Velko/8-bit-CPU/hardware/pcb/register/register.kicad_pcb

## KiCad design hardware/pcb/register/register.kicad_pcb (2020-12-29)

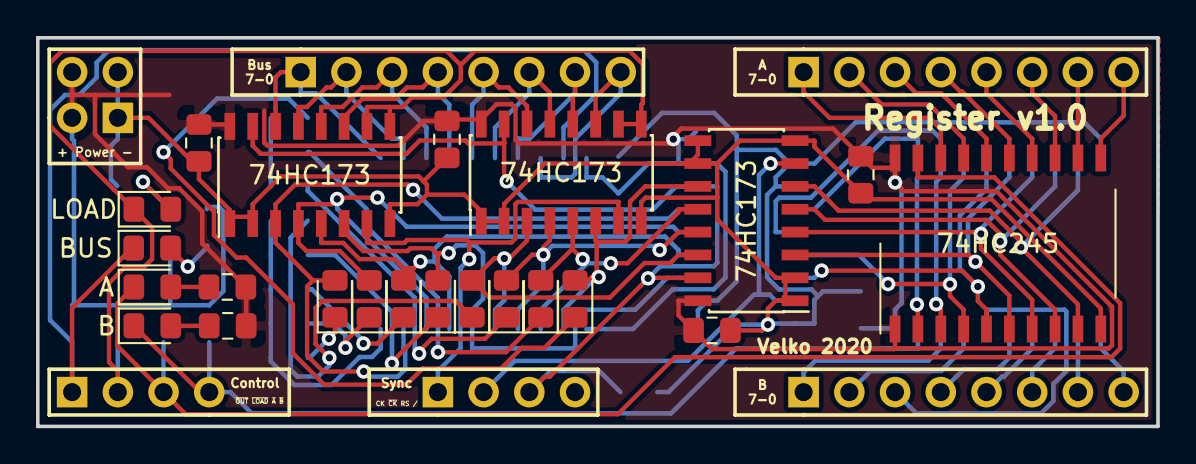
[picture p21: board register.kicad_pcb from above]

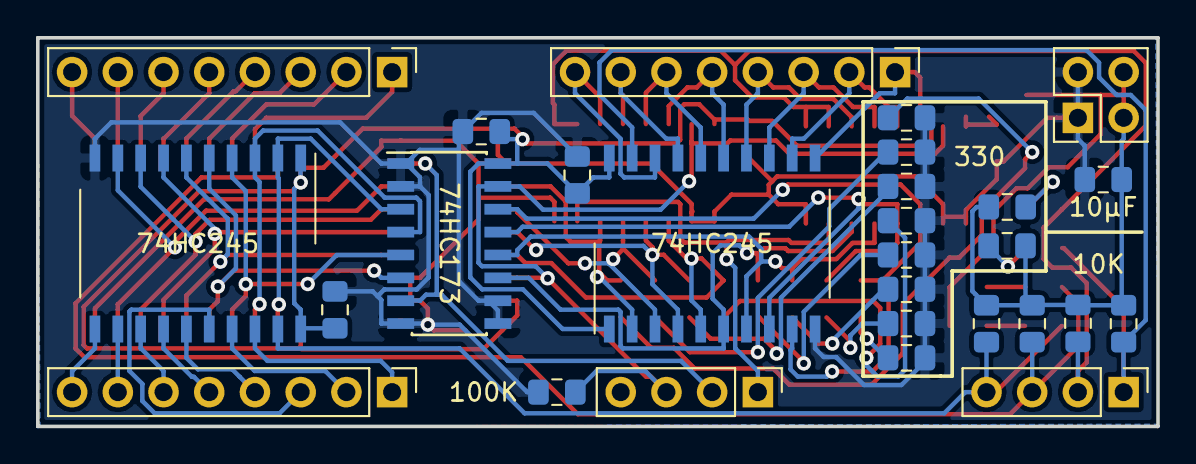
[picture p22: board register.kicad_pcb from below]

Board: 2 copper layers, 62.2 x 21.6 mm, 50 parts (28 on the bottom side), 61 nets.

Parts:
C1, C3, C4, C5, C6, C7, C8: 100nF; C_0805_2012Metric_Pad1.15x1.40mm_HandSolder
C2: 10µF; C_0805_2012Metric_Pad1.15x1.40mm_HandSolder
D1, D2, D3, D4, D5, D6, D7, D8: LED; LED_0805_2012Metric_Pad1.15x1.40mm_HandSolder
D9: LOAD; LED_0805_2012Metric_Pad1.15x1.40mm_HandSolder
D10: BUS; LED_0805_2012Metric_Pad1.15x1.40mm_HandSolder
D11: A; LED_0805_2012Metric_Pad1.15x1.40mm_HandSolder
D12: B; LED_0805_2012Metric_Pad1.15x1.40mm_HandSolder
J1, J5, J6: Conn_01x08_Male; PinHeader_1x08_P2.54mm_Vertical
J2, J3: Conn_01x04_Male; PinHeader_1x04_P2.54mm_Vertical
J4: Conn_01x04_Male; PinHeader_2x02_P2.54mm_Vertical
R1, R2, R3, R4: 10K; R_0805_2012Metric_Pad1.15x1.40mm_HandSolder
R5, R6, R7, R8, R9, R10, R11, R12, R14, R15, R16, R17: 330; R_0805_2012Metric_Pad1.15x1.40mm_HandSolder
R13: 100K; R_0805_2012Metric_Pad1.15x1.40mm_HandSolder
U1, U6, U7: 74HC245; SO-20_12.8x7.5mm_P1.27mm
U2, U3, U4, U5: 74HC173; SOIC-16_3.9x9.9mm_P1.27mm

Connections:
A0: J5.8, U6.11
A1: J5.7, U6.12
A2: J5.6, U6.13
A3: J5.5, U6.14
A4: J5.4, U6.15
A5: J5.3, U6.16
A6: J5.2, U6.17
A7: J5.1, U6.18
B0: J6.8, U7.11
B1: J6.7, U7.12
B2: J6.6, U7.13
B3: J6.5, U7.14
B4: J6.4, U7.15
B5: J6.3, U7.16
B6: J6.2, U7.17
B7: J6.1, U7.18
BUS0: J1.8, U1.18, U2.11
BUS1: J1.7, U1.17, U2.12
BUS2: J1.6, U1.16, U2.13
BUS3: J1.5, U1.15, U2.14
BUS4: J1.4, U1.14, U4.11
BUS5: J1.3, U1.13, U4.12
BUS6: J1.2, U1.12, U4.13
BUS7: J1.1, U1.11, U4.14
CLK: J3.1, U2.7, U4.7
GND: C1.2, C2.2, C3.2, C4.2, C5.2, C6.2, C7.2, C8.2, J4.1, J4.2, R5.1, R6.1, R7.1, R8.1, R9.1, R10.1, R11.1, R12.1, R13.1, U1.10, U2.1, U2.2, U2.8, U3.1, U3.2, U3.8, U3.9, U3.10, U4.1, U4.2, U4.8, U5.1, U5.2, U5.8, U5.9, U5.10, U6.10, U7.10
M0: D1.2, U1.2, U2.6, U3.11
M1: D2.2, U1.3, U2.5, U3.12
M2: D3.2, U1.4, U2.4, U3.13
M3: D4.2, U1.5, U2.3, U3.14
M4: D5.2, U1.6, U4.6, U5.11
M5: D6.2, U1.7, U4.5, U5.12
M6: D7.2, U1.8, U4.4, U5.13
M7: D8.2, U1.9, U4.3, U5.14
unnamed: D1.1, R5.2
unnamed: D2.1, R6.2
unnamed: D3.1, R7.2
unnamed: D4.1, R8.2
unnamed: D5.1, R9.2
unnamed: D6.1, R10.2
unnamed: D7.1, R11.2
unnamed: D8.1, R12.2
unnamed: D9.2, R17.2
unnamed: D10.2, R14.2
unnamed: D11.2, R15.2
unnamed: D12.2, R16.2
RESET: J3.3, R13.2, U2.15, U3.15, U4.15, U5.15
TAP0: U3.6, U6.9, U7.9
TAP1: U3.5, U6.8, U7.8
TAP2: U3.4, U6.7, U7.7
TAP3: U3.3, U6.6, U7.6
TAP4: U5.6, U6.5, U7.5
TAP5: U5.5, U6.4, U7.4
TAP6: U5.4, U6.3, U7.3
TAP7: U5.3, U6.2, U7.2
VCC: C1.1, C2.1, C3.1, C4.1, C5.1, C6.1, C7.1, C8.1, J4.3, J4.4, R1.1, R2.1, R3.2, R4.1, R14.1, R15.1, R16.1, R17.1, U1.1, U1.20, U2.16, U3.16, U4.16, U5.16, U6.1, U6.20, U7.1, U7.20
~A_OUT~: D11.1, J2.3, R2.2, U6.19
~BUS_OUT~: D10.1, J2.1, R1.2, U1.19
~B_OUT~: D12.1, J2.4, R4.2, U7.19
~CLK~: J3.2, U3.7, U5.7
~LOAD~: D9.1, J2.2, R3.1, U2.9, U2.10, U4.9, U4.10
