Velko/8-bit-CPU/hardware/pcb/eeprom_burner/eeprom_burner.kicad_pcb

## KiCad design hardware/pcb/eeprom_burner/eeprom_burner.kicad_pcb (2020-12-29)

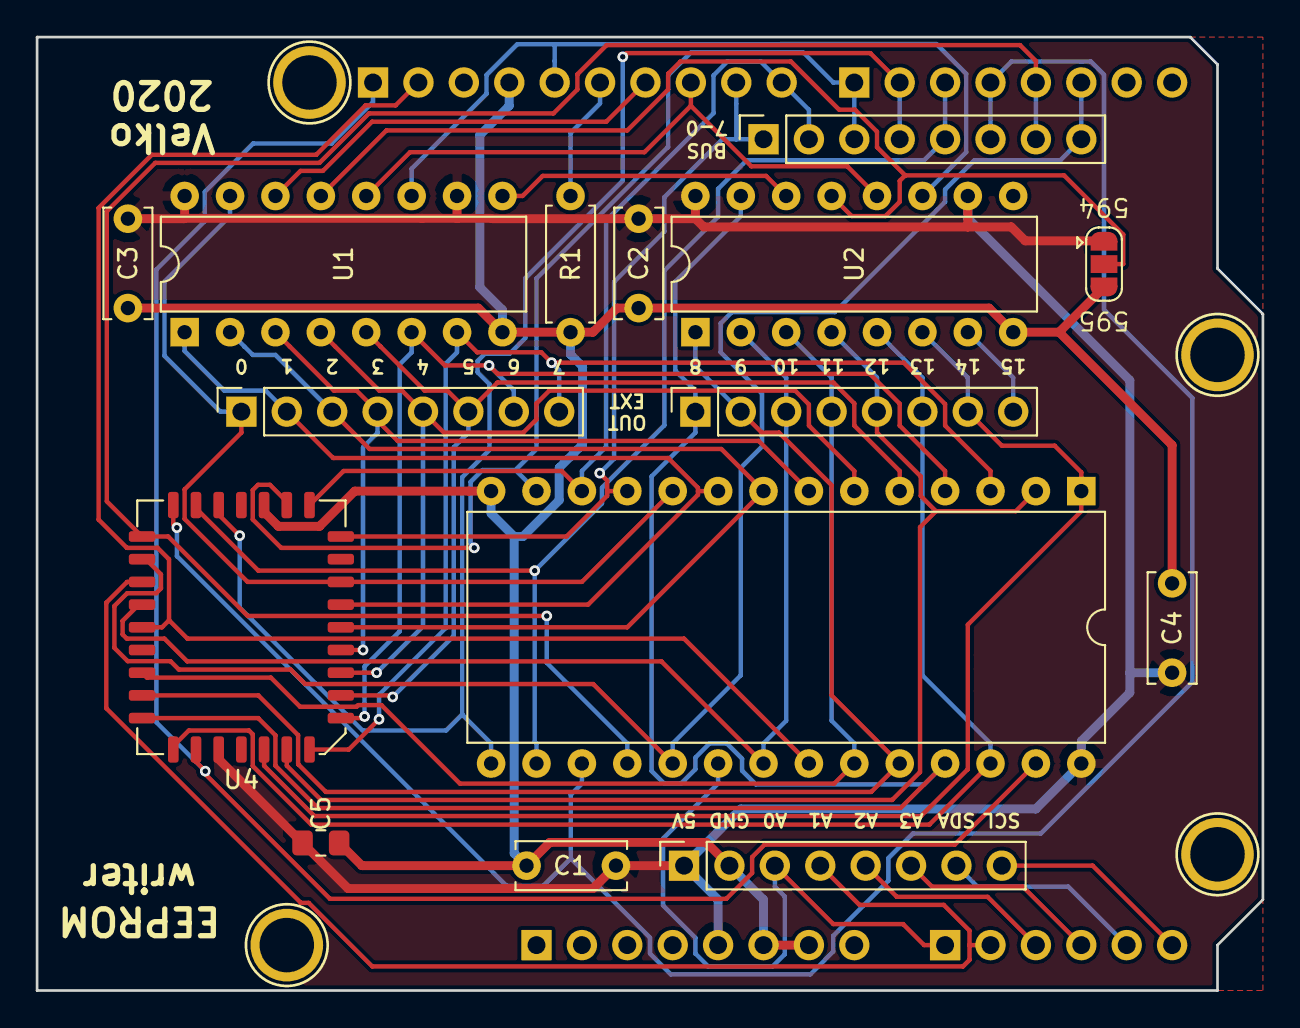
[picture p23: board eeprom_burner.kicad_pcb from above]

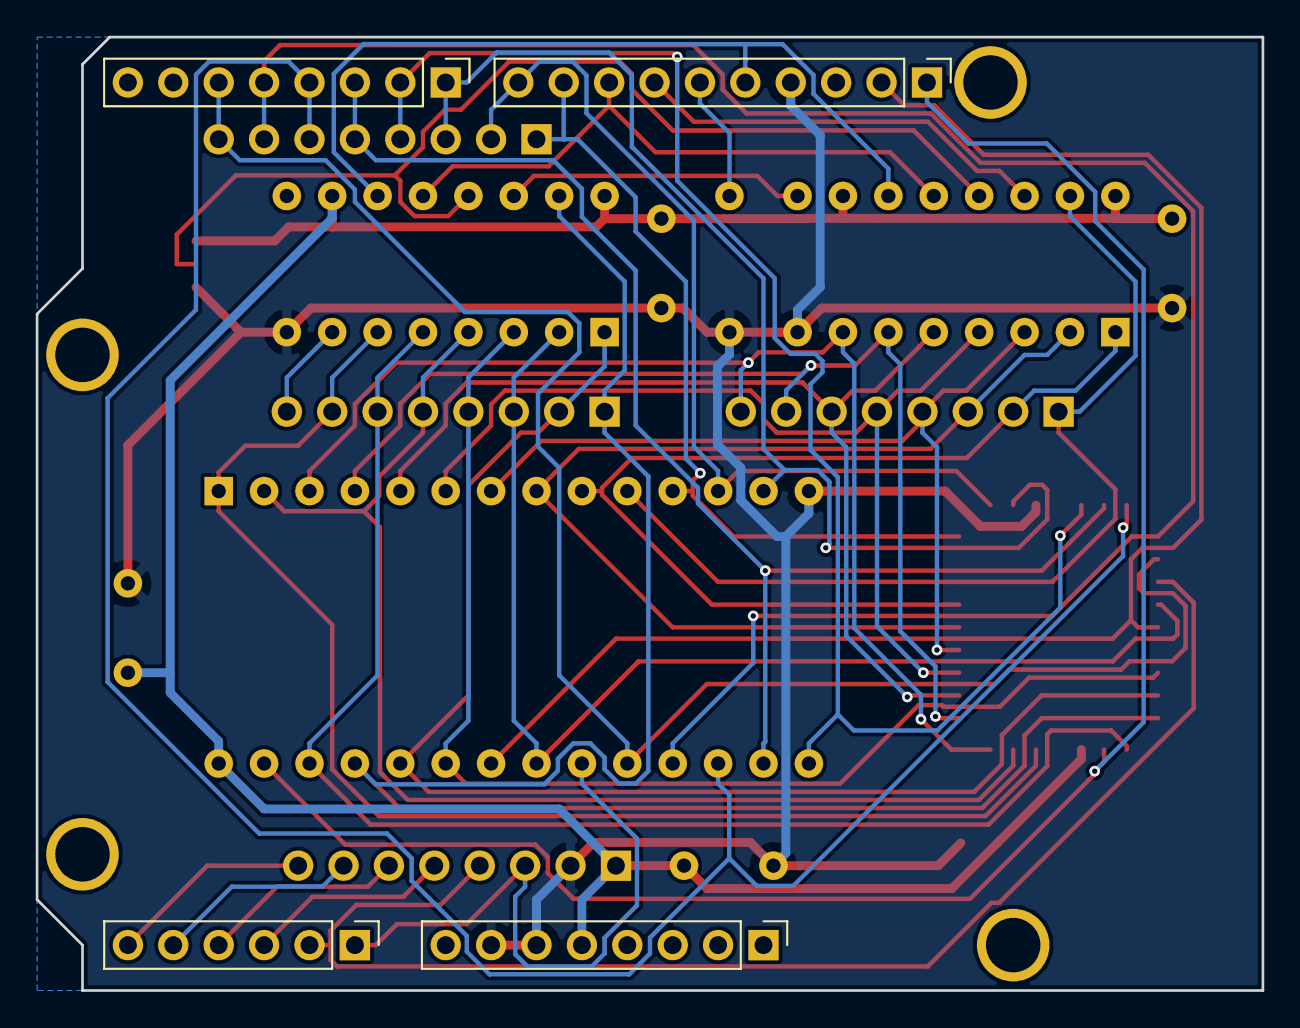
[picture p24: board eeprom_burner.kicad_pcb from below]

Board: 2 copper layers, 68.6 x 53.3 mm, 23 parts (4 on the bottom side), 40 nets.

Parts:
C1, C2, C3, C4: 100nF; C_Disc_D6.0mm_W2.5mm_P5.00mm
C5: 100nF; C_0805_2012Metric_Pad1.15x1.40mm_HandSolder
J1, J2, J3: Conn_01x08; PinSocket_1x08_P2.54mm_Vertical
J4: Conn_01x06; PinSocket_1x08_P2.54mm_Vertical
JP1: SolderJumper_3_Open; SolderJumper-3_P1.3mm_Open_RoundedPad1.0x1.5mm
P1: Power; PinHeader_1x08_P2.54mm_Vertical
P2: Analog; PinHeader_1x06_P2.54mm_Vertical
P3: Digital; PinHeader_1x10_P2.54mm_Vertical
P4: Digital; PinHeader_1x08_P2.54mm_Vertical
P5, P6, P7, P8: CONN_01X01; Arduino_1pin
R1: 10K; R_Axial_DIN0207_L6.3mm_D2.5mm_P7.62mm_Horizontal
U1, U2: 74HC595; DIP-16_W7.62mm
U3: 28C256; DIP-28_W15.24mm
U4: 28C256J; PLCC-32_11.4x14.0mm_P1.27mm

Connections:
+5V: C1.1, C2.1, C3.1, C4.1, C5.1, J4.1, JP1.1, P1.5, U1.10, U1.16, U2.10, U2.16, U3.28, U4.32
A0: J1.1, U1.15, U3.10, U4.11
A1: J1.2, U1.1, U3.9, U4.10
A2: J1.3, U1.2, U3.8, U4.9
A3: J1.4, U1.3, U3.7, U4.8
A4: J1.5, U1.4, U3.6, U4.7
A5: J1.6, U1.5, U3.5, U4.6
A6: J1.7, U1.6, U3.4, U4.5
A7: J1.8, U1.7, U3.3, U4.4
A8: J2.1, U2.15, U3.25, U4.29
A9: J2.2, U2.1, U3.24, U4.28
A10: J2.3, U2.2, U3.21, U4.24
A11: J2.4, U2.3, U3.23, U4.27
A12: J2.5, U2.4, U3.2, U4.3
A13: J2.6, U2.5, U3.26, U4.30
A14: J2.7, U2.6, U3.1, U4.2
A15: J2.8, U2.7
D0: J3.1, P3.9, U3.11, U4.13
D1: J3.2, P3.10, U3.12, U4.14
D2: J3.3, P4.1, U3.13, U4.15
D3: J3.4, P4.2, U3.15, U4.18
D4: J3.5, P4.3, U3.16, U4.19
D5: J3.6, P4.4, U3.17, U4.20
D6: J3.7, P4.5, U3.18, U4.21
D7: J3.8, P4.6, U3.19, U4.22
E0: J4.3, P2.1, U3.20
E1: J4.4, P2.2, U4.23
E2: J4.5, P2.3
E3: J4.6, P2.4
E4: J4.7, P2.5
E5: J4.8, P2.6
GND: C1.2, C2.2, C3.2, C4.2, C5.2, J4.2, JP1.3, P1.6, P1.7, P3.4, R1.2, U1.8, U2.8, U3.14, U4.16
LATCH: P3.8, U1.12, U2.12
MISO: P3.6, R1.1
MOSI: P3.7, U1.14
unnamed: JP1.2, U1.13, U2.13
unnamed: U1.9, U2.14
SCK: P3.5, U1.11, U2.11
~OE~: P3.2, U3.22, U4.25
~WE~: P3.1, U3.27, U4.31
