Velko/8-bit-CPU/hardware/pcb/clock/clock.kicad_pcb

## KiCad design hardware/pcb/clock/clock.kicad_pcb (2020-06-21)

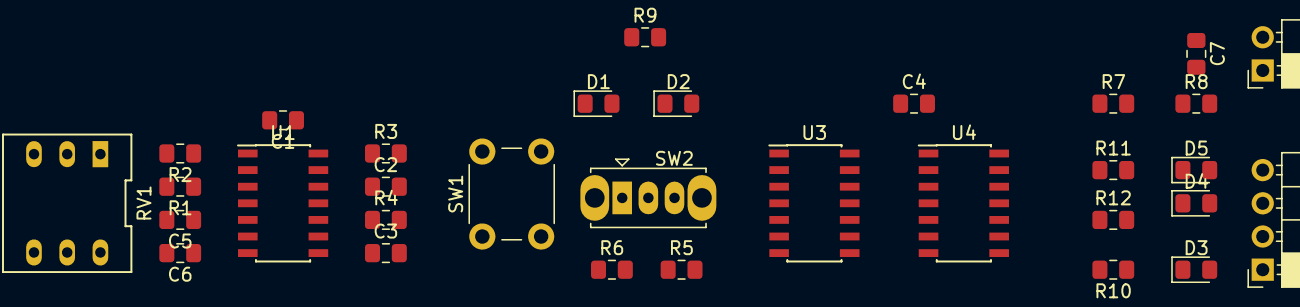
[picture p25: board clock.kicad_pcb from above]

Board: 2 copper layers, 32 parts (0 on the bottom side), 26 nets, no tracks yet.

Parts:
C1, C3, C4, C7: 100nF; C_0805_2012Metric_Pad1.15x1.40mm_HandSolder
C2, C5: 10nF; C_0805_2012Metric_Pad1.15x1.40mm_HandSolder
C6: 1μF; C_0805_2012Metric_Pad1.15x1.40mm_HandSolder
D1, D2, D3, D4, D5: LED; LED_0805_2012Metric_Pad1.15x1.40mm_HandSolder
J1: 01x02_F; PinSocket_1x02_P2.54mm_Horizontal
J2: 01x04_F; PinSocket_1x04_P2.54mm_Horizontal
R1, R2, R3: 1K; R_0805_2012Metric_Pad1.15x1.40mm_HandSolder
R4: 1M; R_0805_2012Metric_Pad1.15x1.40mm_HandSolder
R5, R6, R7, R8: 10K; R_0805_2012Metric_Pad1.15x1.40mm_HandSolder
R9, R10, R11, R12: 330; R_0805_2012Metric_Pad1.15x1.40mm_HandSolder
RV1: 1M; POT_DIP_Dual_Vert
SW1: SW_Push; SW_PUSH_6mm
SW2: SW_SPDT; SW_Slide_1P2T_CK_OS102011MS2Q
U1: TLC556; SOIC-14_3.9x8.7mm_P1.27mm
U3: 74HC02; SOIC-14_3.9x8.7mm_P1.27mm
U4: 74HC00; SOIC-14_3.9x8.7mm_P1.27mm

Connections:
CLK: D3.1, J2.1, U3.5, U3.6, U4.8
GND: C1.2, C2.2, C3.2, C4.2, C5.2, C6.2, C7.2, J1.1, R5.2, R6.2, R8.2, R9.2, R10.2, R11.2, SW1.1, U1.7, U3.2, U3.3, U3.7, U4.7
HLT: D4.1, J2.3, R8.1, U4.13
unnamed: C2.1, U1.11
unnamed: C3.1, R4.2, U1.12, U1.13
unnamed: C5.1, U1.3
unnamed: C6.1, RV1.1, U1.2, U1.6
unnamed: D1.1, U3.9, U3.13, U4.2
unnamed: D1.2, D2.2, R9.1
unnamed: D2.1, U3.10, U3.11, U4.5
unnamed: D3.2, R10.1
unnamed: D4.2, R11.1
unnamed: D5.1, R12.2
unnamed: R1.2, R2.2, U1.1
unnamed: R2.1, RV1.2
unnamed: R3.2, SW1.2, U1.8
unnamed: R5.1, SW2.3, U3.12
unnamed: R6.1, SW2.1, U3.8
unnamed: U1.5, U4.1
unnamed: U1.9, U4.4
unnamed: U1.4, U1.10, U4.11
unnamed: U4.3, U4.9
unnamed: U4.6, U4.10
VCC: C1.1, C4.1, C7.1, J1.2, R1.1, R3.1, R4.1, R7.1, R12.1, SW2.2, U1.14, U3.14, U4.14
~CLK~: J2.2, U3.4
~WAKE~: D5.2, J2.4, R7.2, U4.12
