Velko/8-bit-CPU/turbo/core/src/runtime_state.rs

use crate::{TrapReason, IOPorts};
use crate::flags::Flags;
use crate::router::{MainBusSource, ALULSource, ALURSource, AddressBusSource, FlagsSource};
use crate::router::DeviceMap;

pub struct BusValue<TSource, TValue> {
    pub source: Option<TSource>,
    pub value: TValue,
}

pub struct BusValues {
    pub main_bus: BusValue<MainBusSource, Option<u8>>,
    pub alu_l: BusValue<ALULSource, Option<u8>>,
    pub alu_r: BusValue<ALURSource, Option<u8>>,
    pub address_bus: BusValue<AddressBusSource, Option<u16>>,
    pub flags: BusValue<FlagsSource, ALUFlags>,
    pub injected_main_bus_value: Option<u8>,
    pub injected_address_bus_value: Option<u16>,
    pub th_reg_val: u8,
    pub tl_reg_val: u8,
    pub trap_reason: Option<TrapReason>,
}

impl BusValues {
    pub fn new() -> Self {
        Self {
            main_bus: BusValue { source: None, value: None },
            alu_l: BusValue { source: None, value: None },
            alu_r: BusValue { source: None, value: None },
            address_bus: BusValue { source: None, value: None },
            flags: BusValue { source: None, value: ALUFlags { carry: None, overflow: None } },
            injected_main_bus_value: None,
            injected_address_bus_value: None,
            th_reg_val: 0,
            tl_reg_val: 0,
            trap_reason: None,
        }
    }

    pub fn resolve<P: IOPorts>(&mut self, devices: &DeviceMap<P>) {
        self.alu_l.value = self.alu_l.source.map(|source| devices.get_alu_l_value(source, self));
        self.alu_r.value = self.alu_r.source.map(|source| devices.get_alu_r_value(source, self));
        self.address_bus.value = self.injected_address_bus_value.or_else(|| self.address_bus.source.map(|source| devices.get_address_bus_value(source, self)));
        self.main_bus.value = self.injected_main_bus_value.or_else(|| self.main_bus.source.map(|source| devices.get_main_bus_value(source, self)));
        self.flags.value = self.flags.source.map(|source| devices.get_flags_value(source, self)).unwrap_or(ALUFlags { carry: None, overflow: None });
    }
}

pub struct ALUFlags {
    pub carry: Option<Flags>,
    pub overflow: Option<Flags>,
}
