Velko/8-bit-CPU/emulator/cpu-modules/io_control.v

module io_control (
    inout [7:0] main_bus,
    input rst,
    input clk,

    input loadn,
    input from_devn,
    input to_devn,

    output [7:0] sel_x,
    output [7:0] sel_y,
    output [7:0] sel_p,
    inout [7:0] io_bus
);

    wire [7:0] port_addr;

    dff_377 addr_reg (
        .cp(clk),
        .en(loadn),
        .d(main_bus),
        .q(port_addr)
    );

    demux_138 sel_mux_x (
        .a(port_addr[2:0]),
        .e1n(from_devn && to_devn),
        .e2n(1'b0),
        .e3(1'b1),
        .y(sel_x)
    );

    demux_138 sel_mux_y (
        .a(port_addr[6:4]),
        .e1n(from_devn && to_devn),
        .e2n(1'b0),
        .e3(1'b1),
        .y(sel_y)
    );

    buffer_245 io_buffer (
        .a(main_bus),
        .b(io_bus),
        .dir(from_devn),
        .oen(from_devn && to_devn)
    );

    assign sel_p = port_addr;

endmodule
