Velko/8-bit-CPU/include/microcode.c

#include "microcode.h"

const cword_t op_fetch[] = {0x07bd5889};

const struct op_microcode microcode[] PROGMEM = {

    /* 00 nop        */
    { .default_steps = {0x07ff58ff},},

    /* 01 ldi_A_imm  */
    { .default_steps = {0x07bd5809},},

    /* 02 ldi_B_imm  */
    { .default_steps = {0x07bd5819},},

    /* 03 ldi_C_imm  */
    { .default_steps = {0x07bd5829},},

    /* 04 ldi_D_imm  */
    { .default_steps = {0x07bd5839},},

    /* 05 ldi_F_imm  */
    { .default_steps = {0x07bd5879},},

    /* 06 hlt        */
    { .default_steps = {0x03ff58ff},},

    /* 07 add_A_A    */
    { .default_steps = {0x07ff0005},},

    /* 08 add_A_B    */
    { .default_steps = {0x07ff0405},},

    /* 09 add_A_C    */
    { .default_steps = {0x07ff0805},},

    /* 0a add_A_D    */
    { .default_steps = {0x07ff0c05},},

    /* 0b add_B_A    */
    { .default_steps = {0x07ff0115},},

    /* 0c add_B_B    */
    { .default_steps = {0x07ff0515},},

    /* 0d add_B_C    */
    { .default_steps = {0x07ff0915},},

    /* 0e add_B_D    */
    { .default_steps = {0x07ff0d15},},

    /* 0f add_C_A    */
    { .default_steps = {0x07ff0225},},

    /* 10 add_C_B    */
    { .default_steps = {0x07ff0625},},

    /* 11 add_C_C    */
    { .default_steps = {0x07ff0a25},},

    /* 12 add_C_D    */
    { .default_steps = {0x07ff0e25},},

    /* 13 add_D_A    */
    { .default_steps = {0x07ff0335},},

    /* 14 add_D_B    */
    { .default_steps = {0x07ff0735},},

    /* 15 add_D_C    */
    { .default_steps = {0x07ff0b35},},

    /* 16 add_D_D    */
    { .default_steps = {0x07ff0f35},},

    /* 17 adc_A_A    */
    { .default_steps = {0x07ff0005},
      .f_alt = {
          /* mask: -C-- value: -C-- */
          { .mask = 0x04, .value = 0x04,
            .steps = {0x07ff8005},
          },
      },
    },

    /* 18 adc_A_B    */
    { .default_steps = {0x07ff0405},
      .f_alt = {
          /* mask: -C-- value: -C-- */
          { .mask = 0x04, .value = 0x04,
            .steps = {0x07ff8405},
          },
      },
    },

    /* 19 adc_A_C    */
    { .default_steps = {0x07ff0805},
      .f_alt = {
          /* mask: -C-- value: -C-- */
          { .mask = 0x04, .value = 0x04,
            .steps = {0x07ff8805},
          },
      },
    },

    /* 1a adc_A_D    */
    { .default_steps = {0x07ff0c05},
      .f_alt = {
          /* mask: -C-- value: -C-- */
          { .mask = 0x04, .value = 0x04,
            .steps = {0x07ff8c05},
          },
      },
    },

    /* 1b adc_B_A    */
    { .default_steps = {0x07ff0115},
      .f_alt = {
          /* mask: -C-- value: -C-- */
          { .mask = 0x04, .value = 0x04,
            .steps = {0x07ff8115},
          },
      },
    },

    /* 1c adc_B_B    */
    { .default_steps = {0x07ff0515},
      .f_alt = {
          /* mask: -C-- value: -C-- */
          { .mask = 0x04, .value = 0x04,
            .steps = {0x07ff8515},
          },
      },
    },

    /* 1d adc_B_C    */
    { .default_steps = {0x07ff0915},
      .f_alt = {
          /* mask: -C-- value: -C-- */
          { .mask = 0x04, .value = 0x04,
            .steps = {0x07ff8915},
          },
      },
    },

    /* 1e adc_B_D    */
    { .default_steps = {0x07ff0d15},
      .f_alt = {
          /* mask: -C-- value: -C-- */
          { .mask = 0x04, .value = 0x04,
            .steps = {0x07ff8d15},
          },
      },
    },

    /* 1f adc_C_A    */
    { .default_steps = {0x07ff0225},
      .f_alt = {
          /* mask: -C-- value: -C-- */
          { .mask = 0x04, .value = 0x04,
            .steps = {0x07ff8225},
          },
      },
    },

    /* 20 adc_C_B    */
    { .default_steps = {0x07ff0625},
      .f_alt = {
          /* mask: -C-- value: -C-- */
          { .mask = 0x04, .value = 0x04,
            .steps = {0x07ff8625},
          },
      },
    },

    /* 21 adc_C_C    */
    { .default_steps = {0x07ff0a25},
      .f_alt = {
          /* mask: -C-- value: -C-- */
          { .mask = 0x04, .value = 0x04,
            .steps = {0x07ff8a25},
          },
      },
    },

    /* 22 adc_C_D    */
    { .default_steps = {0x07ff0e25},
      .f_alt = {
          /* mask: -C-- value: -C-- */
          { .mask = 0x04, .value = 0x04,
            .steps = {0x07ff8e25},
          },
      },
    },

    /* 23 adc_D_A    */
    { .default_steps = {0x07ff0335},
      .f_alt = {
          /* mask: -C-- value: -C-- */
          { .mask = 0x04, .value = 0x04,
            .steps = {0x07ff8335},
          },
      },
    },

    /* 24 adc_D_B    */
    { .default_steps = {0x07ff0735},
      .f_alt = {
          /* mask: -C-- value: -C-- */
          { .mask = 0x04, .value = 0x04,
            .steps = {0x07ff8735},
          },
      },
    },

    /* 25 adc_D_C    */
    { .default_steps = {0x07ff0b35},
      .f_alt = {
          /* mask: -C-- value: -C-- */
          { .mask = 0x04, .value = 0x04,
            .steps = {0x07ff8b35},
          },
      },
    },

    /* 26 adc_D_D    */
    { .default_steps = {0x07ff0f35},
      .f_alt = {
          /* mask: -C-- value: -C-- */
          { .mask = 0x04, .value = 0x04,
            .steps = {0x07ff8f35},
          },
      },
    },

    /* 27 sub_A_B    */
    { .default_steps = {0x07ff2405},},

    /* 28 sub_A_C    */
    { .default_steps = {0x07ff2805},},

    /* 29 sub_A_D    */
    { .default_steps = {0x07ff2c05},},

    /* 2a sub_B_A    */
    { .default_steps = {0x07ff2115},},

    /* 2b sub_B_C    */
    { .default_steps = {0x07ff2915},},

    /* 2c sub_B_D    */
    { .default_steps = {0x07ff2d15},},

    /* 2d sub_C_A    */
    { .default_steps = {0x07ff2225},},

    /* 2e sub_C_B    */
    { .default_steps = {0x07ff2625},},

    /* 2f sub_C_D    */
    { .default_steps = {0x07ff2e25},},

    /* 30 sub_D_A    */
    { .default_steps = {0x07ff2335},},

    /* 31 sub_D_B    */
    { .default_steps = {0x07ff2735},},

    /* 32 sub_D_C    */
    { .default_steps = {0x07ff2b35},},

    /* 33 sbb_A_B    */
    { .default_steps = {0x07ff2405},
      .f_alt = {
          /* mask: -C-- value: -C-- */
          { .mask = 0x04, .value = 0x04,
            .steps = {0x07ffa405},
          },
      },
    },

    /* 34 sbb_A_C    */
    { .default_steps = {0x07ff2805},
      .f_alt = {
          /* mask: -C-- value: -C-- */
          { .mask = 0x04, .value = 0x04,
            .steps = {0x07ffa805},
          },
      },
    },

    /* 35 sbb_A_D    */
    { .default_steps = {0x07ff2c05},
      .f_alt = {
          /* mask: -C-- value: -C-- */
          { .mask = 0x04, .value = 0x04,
            .steps = {0x07ffac05},
          },
      },
    },

    /* 36 sbb_B_A    */
    { .default_steps = {0x07ff2115},
      .f_alt = {
          /* mask: -C-- value: -C-- */
          { .mask = 0x04, .value = 0x04,
            .steps = {0x07ffa115},
          },
      },
    },

    /* 37 sbb_B_C    */
    { .default_steps = {0x07ff2915},
      .f_alt = {
          /* mask: -C-- value: -C-- */
          { .mask = 0x04, .value = 0x04,
            .steps = {0x07ffa915},
          },
      },
    },

    /* 38 sbb_B_D    */
    { .default_steps = {0x07ff2d15},
      .f_alt = {
          /* mask: -C-- value: -C-- */
          { .mask = 0x04, .value = 0x04,
            .steps = {0x07ffad15},
          },
      },
    },

    /* 39 sbb_C_A    */
    { .default_steps = {0x07ff2225},
      .f_alt = {
          /* mask: -C-- value: -C-- */
          { .mask = 0x04, .value = 0x04,
            .steps = {0x07ffa225},
          },
      },
    },

    /* 3a sbb_C_B    */
    { .default_steps = {0x07ff2625},
      .f_alt = {
          /* mask: -C-- value: -C-- */
          { .mask = 0x04, .value = 0x04,
            .steps = {0x07ffa625},
          },
      },
    },

    /* 3b sbb_C_D    */
    { .default_steps = {0x07ff2e25},
      .f_alt = {
          /* mask: -C-- value: -C-- */
          { .mask = 0x04, .value = 0x04,
            .steps = {0x07ffae25},
          },
      },
    },

    /* 3c sbb_D_A    */
    { .default_steps = {0x07ff2335},
      .f_alt = {
          /* mask: -C-- value: -C-- */
          { .mask = 0x04, .value = 0x04,
            .steps = {0x07ffa335},
          },
      },
    },

    /* 3d sbb_D_B    */
    { .default_steps = {0x07ff2735},
      .f_alt = {
          /* mask: -C-- value: -C-- */
          { .mask = 0x04, .value = 0x04,
            .steps = {0x07ffa735},
          },
      },
    },

    /* 3e sbb_D_C    */
    { .default_steps = {0x07ff2b35},
      .f_alt = {
          /* mask: -C-- value: -C-- */
          { .mask = 0x04, .value = 0x04,
            .steps = {0x07ffab35},
          },
      },
    },

    /* 3f and_A_B    */
    { .default_steps = {0x07ff0406},},

    /* 40 and_A_C    */
    { .default_steps = {0x07ff0806},},

    /* 41 and_A_D    */
    { .default_steps = {0x07ff0c06},},

    /* 42 and_B_A    */
    { .default_steps = {0x07ff0116},},

    /* 43 and_B_C    */
    { .default_steps = {0x07ff0916},},

    /* 44 and_B_D    */
    { .default_steps = {0x07ff0d16},},

    /* 45 and_C_A    */
    { .default_steps = {0x07ff0226},},

    /* 46 and_C_B    */
    { .default_steps = {0x07ff0626},},

    /* 47 and_C_D    */
    { .default_steps = {0x07ff0e26},},

    /* 48 and_D_A    */
    { .default_steps = {0x07ff0336},},

    /* 49 and_D_B    */
    { .default_steps = {0x07ff0736},},

    /* 4a and_D_C    */
    { .default_steps = {0x07ff0b36},},

    /* 4b or_A_B     */
    { .default_steps = {0x07ff040d},},

    /* 4c or_A_C     */
    { .default_steps = {0x07ff080d},},

    /* 4d or_A_D     */
    { .default_steps = {0x07ff0c0d},},

    /* 4e or_B_A     */
    { .default_steps = {0x07ff011d},},

    /* 4f or_B_C     */
    { .default_steps = {0x07ff091d},},

    /* 50 or_B_D     */
    { .default_steps = {0x07ff0d1d},},

    /* 51 or_C_A     */
    { .default_steps = {0x07ff022d},},

    /* 52 or_C_B     */
    { .default_steps = {0x07ff062d},},

    /* 53 or_C_D     */
    { .default_steps = {0x07ff0e2d},},

    /* 54 or_D_A     */
    { .default_steps = {0x07ff033d},},

    /* 55 or_D_B     */
    { .default_steps = {0x07ff073d},},

    /* 56 or_D_C     */
    { .default_steps = {0x07ff0b3d},},

    /* 57 xor_A_B    */
    { .default_steps = {0x07ff040a},},

    /* 58 xor_A_C    */
    { .default_steps = {0x07ff080a},},

    /* 59 xor_A_D    */
    { .default_steps = {0x07ff0c0a},},

    /* 5a xor_B_A    */
    { .default_steps = {0x07ff011a},},

    /* 5b xor_B_C    */
    { .default_steps = {0x07ff091a},},

    /* 5c xor_B_D    */
    { .default_steps = {0x07ff0d1a},},

    /* 5d xor_C_A    */
    { .default_steps = {0x07ff022a},},

    /* 5e xor_C_B    */
    { .default_steps = {0x07ff062a},},

    /* 5f xor_C_D    */
    { .default_steps = {0x07ff0e2a},},

    /* 60 xor_D_A    */
    { .default_steps = {0x07ff033a},},

    /* 61 xor_D_B    */
    { .default_steps = {0x07ff073a},},

    /* 62 xor_D_C    */
    { .default_steps = {0x07ff0b3a},},

    /* 63 not_A      */
    { .default_steps = {0x07ff140a},},

    /* 64 not_B      */
    { .default_steps = {0x07ff151a},},

    /* 65 not_C      */
    { .default_steps = {0x07ff162a},},

    /* 66 not_D      */
    { .default_steps = {0x07ff173a},},

    /* 67 clr_A      */
    { .default_steps = {0x07ff000a},},

    /* 68 clr_B      */
    { .default_steps = {0x07ff051a},},

    /* 69 clr_C      */
    { .default_steps = {0x07ff0a2a},},

    /* 6a clr_D      */
    { .default_steps = {0x07ff0f3a},},

    /* 6b inc_A      */
    { .default_steps = {0x07ff9805},},

    /* 6c inc_B      */
    { .default_steps = {0x07ff9915},},

    /* 6d inc_C      */
    { .default_steps = {0x07ff9a25},},

    /* 6e inc_D      */
    { .default_steps = {0x07ff9b35},},

    /* 6f dec_A      */
    { .default_steps = {0x07ffb805},},

    /* 70 dec_B      */
    { .default_steps = {0x07ffb915},},

    /* 71 dec_C      */
    { .default_steps = {0x07ffba25},},

    /* 72 dec_D      */
    { .default_steps = {0x07ffbb35},},

    /* 73 shr_A      */
    { .default_steps = {0x07ff1807},},

    /* 74 shr_B      */
    { .default_steps = {0x07ff1917},},

    /* 75 shr_C      */
    { .default_steps = {0x07ff1a27},},

    /* 76 shr_D      */
    { .default_steps = {0x07ff1b37},},

    /* 77 ror_A      */
    { .default_steps = {0x07ff1807},
      .f_alt = {
          /* mask: -C-- value: -C-- */
          { .mask = 0x04, .value = 0x04,
            .steps = {0x07ff9807},
          },
      },
    },

    /* 78 ror_B      */
    { .default_steps = {0x07ff1917},
      .f_alt = {
          /* mask: -C-- value: -C-- */
          { .mask = 0x04, .value = 0x04,
            .steps = {0x07ff9917},
          },
      },
    },

    /* 79 ror_C      */
    { .default_steps = {0x07ff1a27},
      .f_alt = {
          /* mask: -C-- value: -C-- */
          { .mask = 0x04, .value = 0x04,
            .steps = {0x07ff9a27},
          },
      },
    },

    /* 7a ror_D      */
    { .default_steps = {0x07ff1b37},
      .f_alt = {
          /* mask: -C-- value: -C-- */
          { .mask = 0x04, .value = 0x04,
            .steps = {0x07ff9b37},
          },
      },
    },

    /* 7b asr_A      */
    { .default_steps = {0x07ff18f0, 0x07ff1807},
      .f_alt = {
          /* mask: ---N value: ---N */
          { .mask = 0x01, .value = 0x01,
            .steps = {0x07ff18f0, 0x07ff9807},
          },
      },
    },

    /* 7c asr_B      */
    { .default_steps = {0x07ff18f1, 0x07ff1917},
      .f_alt = {
          /* mask: ---N value: ---N */
          { .mask = 0x01, .value = 0x01,
            .steps = {0x07ff18f1, 0x07ff9917},
          },
      },
    },

    /* 7d asr_C      */
    { .default_steps = {0x07ff18f2, 0x07ff1a27},
      .f_alt = {
          /* mask: ---N value: ---N */
          { .mask = 0x01, .value = 0x01,
            .steps = {0x07ff18f2, 0x07ff9a27},
          },
      },
    },

    /* 7e asr_D      */
    { .default_steps = {0x07ff18f3, 0x07ff1b37},
      .f_alt = {
          /* mask: ---N value: ---N */
          { .mask = 0x01, .value = 0x01,
            .steps = {0x07ff18f3, 0x07ff9b37},
          },
      },
    },

    /* 7f swap_A     */
    { .default_steps = {0x07ff180e},},

    /* 80 swap_B     */
    { .default_steps = {0x07ff191e},},

    /* 81 swap_C     */
    { .default_steps = {0x07ff1a2e},},

    /* 82 swap_D     */
    { .default_steps = {0x07ff1b3e},},

    /* 83 cmp_A_B    */
    { .default_steps = {0x07ff24f5},},

    /* 84 cmp_A_C    */
    { .default_steps = {0x07ff28f5},},

    /* 85 cmp_A_D    */
    { .default_steps = {0x07ff2cf5},},

    /* 86 cmp_B_A    */
    { .default_steps = {0x07ff21f5},},

    /* 87 cmp_B_C    */
    { .default_steps = {0x07ff29f5},},

    /* 88 cmp_B_D    */
    { .default_steps = {0x07ff2df5},},

    /* 89 cmp_C_A    */
    { .default_steps = {0x07ff22f5},},

    /* 8a cmp_C_B    */
    { .default_steps = {0x07ff26f5},},

    /* 8b cmp_C_D    */
    { .default_steps = {0x07ff2ef5},},

    /* 8c cmp_D_A    */
    { .default_steps = {0x07ff23f5},},

    /* 8d cmp_D_B    */
    { .default_steps = {0x07ff27f5},},

    /* 8e cmp_D_C    */
    { .default_steps = {0x07ff2bf5},},

    /* 8f mov_A_B    */
    { .default_steps = {0x07ff5801},},

    /* 90 mov_A_C    */
    { .default_steps = {0x07ff5802},},

    /* 91 mov_A_D    */
    { .default_steps = {0x07ff5803},},

    /* 92 mov_B_A    */
    { .default_steps = {0x07ff5810},},

    /* 93 mov_B_C    */
    { .default_steps = {0x07ff5812},},

    /* 94 mov_B_D    */
    { .default_steps = {0x07ff5813},},

    /* 95 mov_C_A    */
    { .default_steps = {0x07ff5820},},

    /* 96 mov_C_B    */
    { .default_steps = {0x07ff5821},},

    /* 97 mov_C_D    */
    { .default_steps = {0x07ff5823},},

    /* 98 mov_D_A    */
    { .default_steps = {0x07ff5830},},

    /* 99 mov_D_B    */
    { .default_steps = {0x07ff5831},},

    /* 9a mov_D_C    */
    { .default_steps = {0x07ff5832},},

    /* 9b out_imm_A  */
    { .default_steps = {0x07bd5849, 0x07ff5850},},

    /* 9c out_imm_B  */
    { .default_steps = {0x07bd5849, 0x07ff5851},},

    /* 9d out_imm_C  */
    { .default_steps = {0x07bd5849, 0x07ff5852},},

    /* 9e out_imm_D  */
    { .default_steps = {0x07bd5849, 0x07ff5853},},

    /* 9f in_A_imm   */
    { .default_steps = {0x07bd5849, 0x07ff1808},},

    /* a0 in_B_imm   */
    { .default_steps = {0x07bd5849, 0x07ff1818},},

    /* a1 in_C_imm   */
    { .default_steps = {0x07bd5849, 0x07ff1828},},

    /* a2 in_D_imm   */
    { .default_steps = {0x07bd5849, 0x07ff1838},},

    /* a3 st_addr_A  */
    { .default_steps = {0x07bd58b9, 0x07bd58c9, 0x07f85890},},

    /* a4 st_addr_B  */
    { .default_steps = {0x07bd58b9, 0x07bd58c9, 0x07f85891},},

    /* a5 st_addr_C  */
    { .default_steps = {0x07bd58b9, 0x07bd58c9, 0x07f85892},},

    /* a6 st_addr_D  */
    { .default_steps = {0x07bd58b9, 0x07bd58c9, 0x07f85893},},

    /* a7 st_TDP_A_A */
    { .default_steps = {0x07d658f0, 0x07fa5890},},

    /* a8 st_TDP_A_B */
    { .default_steps = {0x07d658f0, 0x07fa5891},},

    /* a9 st_TDP_A_C */
    { .default_steps = {0x07d658f0, 0x07fa5892},},

    /* aa st_TDP_A_D */
    { .default_steps = {0x07d658f0, 0x07fa5893},},

    /* ab st_TDP_B_A */
    { .default_steps = {0x07d658f1, 0x07fa5890},},

    /* ac st_TDP_B_B */
    { .default_steps = {0x07d658f1, 0x07fa5891},},

    /* ad st_TDP_B_C */
    { .default_steps = {0x07d658f1, 0x07fa5892},},

    /* ae st_TDP_B_D */
    { .default_steps = {0x07d658f1, 0x07fa5893},},

    /* af st_TDP_C_A */
    { .default_steps = {0x07d658f2, 0x07fa5890},},

    /* b0 st_TDP_C_B */
    { .default_steps = {0x07d658f2, 0x07fa5891},},

    /* b1 st_TDP_C_C */
    { .default_steps = {0x07d658f2, 0x07fa5892},},

    /* b2 st_TDP_C_D */
    { .default_steps = {0x07d658f2, 0x07fa5893},},

    /* b3 st_TDP_D_A */
    { .default_steps = {0x07d658f3, 0x07fa5890},},

    /* b4 st_TDP_D_B */
    { .default_steps = {0x07d658f3, 0x07fa5891},},

    /* b5 st_TDP_D_C */
    { .default_steps = {0x07d658f3, 0x07fa5892},},

    /* b6 st_TDP_D_D */
    { .default_steps = {0x07d658f3, 0x07fa5893},},

    /* b7 ld_A_addr  */
    { .default_steps = {0x07bd58b9, 0x07bd58c9, 0x07f81809},},

    /* b8 ld_B_addr  */
    { .default_steps = {0x07bd58b9, 0x07bd58c9, 0x07f81819},},

    /* b9 ld_C_addr  */
    { .default_steps = {0x07bd58b9, 0x07bd58c9, 0x07f81829},},

    /* ba ld_D_addr  */
    { .default_steps = {0x07bd58b9, 0x07bd58c9, 0x07f81839},},

    /* bb ld_A_SDP_A */
    { .default_steps = {0x07d158f0, 0x07fa1809},},

    /* bc ld_A_SDP_B */
    { .default_steps = {0x07d158f1, 0x07fa1809},},

    /* bd ld_A_SDP_C */
    { .default_steps = {0x07d158f2, 0x07fa1809},},

    /* be ld_A_SDP_D */
    { .default_steps = {0x07d158f3, 0x07fa1809},},

    /* bf ld_B_SDP_A */
    { .default_steps = {0x07d158f0, 0x07fa1819},},

    /* c0 ld_B_SDP_B */
    { .default_steps = {0x07d158f1, 0x07fa1819},},

    /* c1 ld_B_SDP_C */
    { .default_steps = {0x07d158f2, 0x07fa1819},},

    /* c2 ld_B_SDP_D */
    { .default_steps = {0x07d158f3, 0x07fa1819},},

    /* c3 ld_C_SDP_A */
    { .default_steps = {0x07d158f0, 0x07fa1829},},

    /* c4 ld_C_SDP_B */
    { .default_steps = {0x07d158f1, 0x07fa1829},},

    /* c5 ld_C_SDP_C */
    { .default_steps = {0x07d158f2, 0x07fa1829},},

    /* c6 ld_C_SDP_D */
    { .default_steps = {0x07d158f3, 0x07fa1829},},

    /* c7 ld_D_SDP_A */
    { .default_steps = {0x07d158f0, 0x07fa1839},},

    /* c8 ld_D_SDP_B */
    { .default_steps = {0x07d158f1, 0x07fa1839},},

    /* c9 ld_D_SDP_C */
    { .default_steps = {0x07d158f2, 0x07fa1839},},

    /* ca ld_D_SDP_D */
    { .default_steps = {0x07d158f3, 0x07fa1839},},

    /* cb st_TDP_A   */
    { .default_steps = {0x07be5890},},

    /* cc st_TDP_B   */
    { .default_steps = {0x07be5891},},

    /* cd st_TDP_C   */
    { .default_steps = {0x07be5892},},

    /* ce st_TDP_D   */
    { .default_steps = {0x07be5893},},

    /* cf jmp_addr   */
    { .default_steps = {0x07bd58b9, 0x07bd58c9, 0x07e858ff},},

    /* d0 beq_addr   */
    { .default_steps = {0x07bd58ff, 0x07bd58ff},
      .f_alt = {
          /* mask: --Z- value: --Z- */
          { .mask = 0x02, .value = 0x02,
            .steps = {0x07bd58b9, 0x07bd58c9, 0x07e858ff},
          },
      },
    },

    /* d1 bne_addr   */
    { .default_steps = {0x07bd58ff, 0x07bd58ff},
      .f_alt = {
          /* mask: --Z- value: ---- */
          { .mask = 0x02, .value = 0x00,
            .steps = {0x07bd58b9, 0x07bd58c9, 0x07e858ff},
          },
      },
    },

    /* d2 bcs_addr   */
    { .default_steps = {0x07bd58ff, 0x07bd58ff},
      .f_alt = {
          /* mask: -C-- value: -C-- */
          { .mask = 0x04, .value = 0x04,
            .steps = {0x07bd58b9, 0x07bd58c9, 0x07e858ff},
          },
      },
    },

    /* d3 bcc_addr   */
    { .default_steps = {0x07bd58ff, 0x07bd58ff},
      .f_alt = {
          /* mask: -C-- value: ---- */
          { .mask = 0x04, .value = 0x00,
            .steps = {0x07bd58b9, 0x07bd58c9, 0x07e858ff},
          },
      },
    },

    /* d4 bmi_addr   */
    { .default_steps = {0x07bd58ff, 0x07bd58ff},
      .f_alt = {
          /* mask: ---N value: ---N */
          { .mask = 0x01, .value = 0x01,
            .steps = {0x07bd58b9, 0x07bd58c9, 0x07e858ff},
          },
      },
    },

    /* d5 bpl_addr   */
    { .default_steps = {0x07bd58ff, 0x07bd58ff},
      .f_alt = {
          /* mask: ---N value: ---- */
          { .mask = 0x01, .value = 0x00,
            .steps = {0x07bd58b9, 0x07bd58c9, 0x07e858ff},
          },
      },
    },

    /* d6 push_A     */
    { .default_steps = {0x077b58ff, 0x07fb5890},},

    /* d7 push_B     */
    { .default_steps = {0x077b58ff, 0x07fb5891},},

    /* d8 push_C     */
    { .default_steps = {0x077b58ff, 0x07fb5892},},

    /* d9 push_D     */
    { .default_steps = {0x077b58ff, 0x07fb5893},},

    /* da push_F     */
    { .default_steps = {0x077b58ff, 0x07fb5894},},

    /* db push_LR    */
    { .default_steps = {0x07c458ff, 0x077b58ff, 0x077b589c, 0x07fb589b},},

    /* dc pop_A      */
    { .default_steps = {0x07bb5809},},

    /* dd pop_B      */
    { .default_steps = {0x07bb5819},},

    /* de pop_C      */
    { .default_steps = {0x07bb5829},},

    /* df pop_D      */
    { .default_steps = {0x07bb5839},},

    /* e0 pop_F      */
    { .default_steps = {0x07bb5879},},

    /* e1 pop_LR     */
    { .default_steps = {0x07bb58b9, 0x07bb58c9, 0x07e058ff},},

    /* e2 call_addr  */
    { .default_steps = {0x07bd58b9, 0x07bd58c9, 0x07e558ff, 0x07e858ff},},

    /* e3 ret        */
    { .default_steps = {0x07ec58ff},},

    /* e4 brk        */
    { .default_steps = {0x0fff58ff},},

    /* e5 lea_SP_addr */
    { .default_steps = {0x07bd58b9, 0x07bd58c9, 0x07d858ff},},

    /* e6 ld_A_SP_imm */
    { .default_steps = {0x07bd58b9, 0x17d358fb, 0x07fa1809},},

    /* e7 ld_B_SP_imm */
    { .default_steps = {0x07bd58b9, 0x17d358fb, 0x07fa1819},},

    /* e8 ld_C_SP_imm */
    { .default_steps = {0x07bd58b9, 0x17d358fb, 0x07fa1829},},

    /* e9 ld_D_SP_imm */
    { .default_steps = {0x07bd58b9, 0x17d358fb, 0x07fa1839},},

    /* ea st_SP_imm_A */
    { .default_steps = {0x07bd58b9, 0x17d358fb, 0x07fa5890},},

    /* eb st_SP_imm_B */
    { .default_steps = {0x07bd58b9, 0x17d358fb, 0x07fa5891},},

    /* ec st_SP_imm_C */
    { .default_steps = {0x07bd58b9, 0x17d358fb, 0x07fa5892},},

    /* ed st_SP_imm_D */
    { .default_steps = {0x07bd58b9, 0x17d358fb, 0x07fa5893},},

    /* ee xprefix    */
    { .default_steps = {0x05bd5889, 0x07ff58ff},},

    /* ef jmp_pcrel  */
    { .default_steps = {0x179558f9, 0x07ea58ff},},

    /* f0 beq_pcrel  */
    { .default_steps = {0x07bd58ff},
      .f_alt = {
          /* mask: --Z- value: --Z- */
          { .mask = 0x02, .value = 0x02,
            .steps = {0x179558f9, 0x07ea58ff},
          },
      },
    },

    /* f1 bne_pcrel  */
    { .default_steps = {0x07bd58ff},
      .f_alt = {
          /* mask: --Z- value: ---- */
          { .mask = 0x02, .value = 0x00,
            .steps = {0x179558f9, 0x07ea58ff},
          },
      },
    },

    /* f2 bcs_pcrel  */
    { .default_steps = {0x07bd58ff},
      .f_alt = {
          /* mask: -C-- value: -C-- */
          { .mask = 0x04, .value = 0x04,
            .steps = {0x179558f9, 0x07ea58ff},
          },
      },
    },

    /* f3 bcc_pcrel  */
    { .default_steps = {0x07bd58ff},
      .f_alt = {
          /* mask: -C-- value: ---- */
          { .mask = 0x04, .value = 0x00,
            .steps = {0x179558f9, 0x07ea58ff},
          },
      },
    },

    /* f4 bmi_pcrel  */
    { .default_steps = {0x07bd58ff},
      .f_alt = {
          /* mask: ---N value: ---N */
          { .mask = 0x01, .value = 0x01,
            .steps = {0x179558f9, 0x07ea58ff},
          },
      },
    },

    /* f5 bpl_pcrel  */
    { .default_steps = {0x07bd58ff},
      .f_alt = {
          /* mask: ---N value: ---- */
          { .mask = 0x01, .value = 0x00,
            .steps = {0x179558f9, 0x07ea58ff},
          },
      },
    },

    /* f6 call_pcrel */
    { .default_steps = {0x179558f9, 0x07e558ff, 0x07ea58ff},},

    /* f7 lcmp_A_B   */
    { .default_steps = {0x07ff04f6},},

    /* f8 lcmp_A_C   */
    { .default_steps = {0x07ff08f6},},

    /* f9 lcmp_A_D   */
    { .default_steps = {0x07ff0cf6},},

    /* fa lcmp_B_A   */
    { .default_steps = {0x07ff01f6},},

    /* fb lcmp_B_C   */
    { .default_steps = {0x07ff09f6},},

    /* fc lcmp_B_D   */
    { .default_steps = {0x07ff0df6},},

    /* fd lcmp_C_A   */
    { .default_steps = {0x07ff02f6},},

    /* fe lcmp_C_B   */
    { .default_steps = {0x07ff06f6},},

    /* ff lcmp_C_D   */
    { .default_steps = {0x07ff0ef6},},

    /* 100 lcmp_D_A   */
    { .default_steps = {0x07ff03f6},},

    /* 101 lcmp_D_B   */
    { .default_steps = {0x07ff07f6},},

    /* 102 lcmp_D_C   */
    { .default_steps = {0x07ff0bf6},},

    /* 103 ld_A_SDP   */
    { .default_steps = {0x07b91809},},

    /* 104 ld_B_SDP   */
    { .default_steps = {0x07b91819},},

    /* 105 ld_C_SDP   */
    { .default_steps = {0x07b91829},},

    /* 106 ld_D_SDP   */
    { .default_steps = {0x07b91839},},

    /* 107 lea_SDP_addr */
    { .default_steps = {0x07bd58b9, 0x07bd58c9, 0x07c858ff},},

    /* 108 lea_TDP_addr */
    { .default_steps = {0x07bd58b9, 0x07bd58c9, 0x07f058ff},},

    /* 109 addi_A_imm */
    { .default_steps = {0x07bd5869, 0x07ff1005},},

    /* 10a addi_B_imm */
    { .default_steps = {0x07bd5869, 0x07ff1115},},

    /* 10b addi_C_imm */
    { .default_steps = {0x07bd5869, 0x07ff1225},},

    /* 10c addi_D_imm */
    { .default_steps = {0x07bd5869, 0x07ff1335},},

    /* 10d dummyext_imm */
    { .default_steps = {0x07ff58ff, 0x07ff58ff, 0x07bd5809},},

    /* 10e adci_A_imm */
    { .default_steps = {0x07bd5869, 0x07ff1005},
      .f_alt = {
          /* mask: -C-- value: -C-- */
          { .mask = 0x04, .value = 0x04,
            .steps = {0x07bd5869, 0x07ff9005},
          },
      },
    },

    /* 10f adci_B_imm */
    { .default_steps = {0x07bd5869, 0x07ff1115},
      .f_alt = {
          /* mask: -C-- value: -C-- */
          { .mask = 0x04, .value = 0x04,
            .steps = {0x07bd5869, 0x07ff9115},
          },
      },
    },

    /* 110 adci_C_imm */
    { .default_steps = {0x07bd5869, 0x07ff1225},
      .f_alt = {
          /* mask: -C-- value: -C-- */
          { .mask = 0x04, .value = 0x04,
            .steps = {0x07bd5869, 0x07ff9225},
          },
      },
    },

    /* 111 adci_D_imm */
    { .default_steps = {0x07bd5869, 0x07ff1335},
      .f_alt = {
          /* mask: -C-- value: -C-- */
          { .mask = 0x04, .value = 0x04,
            .steps = {0x07bd5869, 0x07ff9335},
          },
      },
    },

    /* 112 subi_A_imm */
    { .default_steps = {0x07bd5869, 0x07ff3005},},

    /* 113 subi_B_imm */
    { .default_steps = {0x07bd5869, 0x07ff3115},},

    /* 114 subi_C_imm */
    { .default_steps = {0x07bd5869, 0x07ff3225},},

    /* 115 subi_D_imm */
    { .default_steps = {0x07bd5869, 0x07ff3335},},

    /* 116 cmpi_A_imm */
    { .default_steps = {0x07bd5869, 0x07ff30f5},},

    /* 117 cmpi_B_imm */
    { .default_steps = {0x07bd5869, 0x07ff31f5},},

    /* 118 cmpi_C_imm */
    { .default_steps = {0x07bd5869, 0x07ff32f5},},

    /* 119 cmpi_D_imm */
    { .default_steps = {0x07bd5869, 0x07ff33f5},},

    /* 11a sbbi_A_imm */
    { .default_steps = {0x07bd5869, 0x07ff3005},
      .f_alt = {
          /* mask: -C-- value: -C-- */
          { .mask = 0x04, .value = 0x04,
            .steps = {0x07bd5869, 0x07ffb005},
          },
      },
    },

    /* 11b sbbi_B_imm */
    { .default_steps = {0x07bd5869, 0x07ff3115},
      .f_alt = {
          /* mask: -C-- value: -C-- */
          { .mask = 0x04, .value = 0x04,
            .steps = {0x07bd5869, 0x07ffb115},
          },
      },
    },

    /* 11c sbbi_C_imm */
    { .default_steps = {0x07bd5869, 0x07ff3225},
      .f_alt = {
          /* mask: -C-- value: -C-- */
          { .mask = 0x04, .value = 0x04,
            .steps = {0x07bd5869, 0x07ffb225},
          },
      },
    },

    /* 11d sbbi_D_imm */
    { .default_steps = {0x07bd5869, 0x07ff3335},
      .f_alt = {
          /* mask: -C-- value: -C-- */
          { .mask = 0x04, .value = 0x04,
            .steps = {0x07bd5869, 0x07ffb335},
          },
      },
    },

    /* 11e andi_A_imm */
    { .default_steps = {0x07bd5869, 0x07ff1006},},

    /* 11f andi_B_imm */
    { .default_steps = {0x07bd5869, 0x07ff1116},},

    /* 120 andi_C_imm */
    { .default_steps = {0x07bd5869, 0x07ff1226},},

    /* 121 andi_D_imm */
    { .default_steps = {0x07bd5869, 0x07ff1336},},

    /* 122 ori_A_imm  */
    { .default_steps = {0x07bd5869, 0x07ff100d},},

    /* 123 ori_B_imm  */
    { .default_steps = {0x07bd5869, 0x07ff111d},},

    /* 124 ori_C_imm  */
    { .default_steps = {0x07bd5869, 0x07ff122d},},

    /* 125 ori_D_imm  */
    { .default_steps = {0x07bd5869, 0x07ff133d},},

    /* 126 xori_A_imm */
    { .default_steps = {0x07bd5869, 0x07ff100a},},

    /* 127 xori_B_imm */
    { .default_steps = {0x07bd5869, 0x07ff111a},},

    /* 128 xori_C_imm */
    { .default_steps = {0x07bd5869, 0x07ff122a},},

    /* 129 xori_D_imm */
    { .default_steps = {0x07bd5869, 0x07ff133a},},

    /* 12a st_SDP_A_A */
    { .default_steps = {0x07d158f0, 0x07fa5890},},

    /* 12b st_SDP_A_B */
    { .default_steps = {0x07d158f0, 0x07fa5891},},

    /* 12c st_SDP_A_C */
    { .default_steps = {0x07d158f0, 0x07fa5892},},

    /* 12d st_SDP_A_D */
    { .default_steps = {0x07d158f0, 0x07fa5893},},

    /* 12e st_SDP_B_A */
    { .default_steps = {0x07d158f1, 0x07fa5890},},

    /* 12f st_SDP_B_B */
    { .default_steps = {0x07d158f1, 0x07fa5891},},

    /* 130 st_SDP_B_C */
    { .default_steps = {0x07d158f1, 0x07fa5892},},

    /* 131 st_SDP_B_D */
    { .default_steps = {0x07d158f1, 0x07fa5893},},

    /* 132 st_SDP_C_A */
    { .default_steps = {0x07d158f2, 0x07fa5890},},

    /* 133 st_SDP_C_B */
    { .default_steps = {0x07d158f2, 0x07fa5891},},

    /* 134 st_SDP_C_C */
    { .default_steps = {0x07d158f2, 0x07fa5892},},

    /* 135 st_SDP_C_D */
    { .default_steps = {0x07d158f2, 0x07fa5893},},

    /* 136 st_SDP_D_A */
    { .default_steps = {0x07d158f3, 0x07fa5890},},

    /* 137 st_SDP_D_B */
    { .default_steps = {0x07d158f3, 0x07fa5891},},

    /* 138 st_SDP_D_C */
    { .default_steps = {0x07d158f3, 0x07fa5892},},

    /* 139 st_SDP_D_D */
    { .default_steps = {0x07d158f3, 0x07fa5893},},

    /* 13a ld_A_TDP_A */
    { .default_steps = {0x07d658f0, 0x07fa1809},},

    /* 13b ld_A_TDP_B */
    { .default_steps = {0x07d658f1, 0x07fa1809},},

    /* 13c ld_A_TDP_C */
    { .default_steps = {0x07d658f2, 0x07fa1809},},

    /* 13d ld_A_TDP_D */
    { .default_steps = {0x07d658f3, 0x07fa1809},},

    /* 13e ld_B_TDP_A */
    { .default_steps = {0x07d658f0, 0x07fa1819},},

    /* 13f ld_B_TDP_B */
    { .default_steps = {0x07d658f1, 0x07fa1819},},

    /* 140 ld_B_TDP_C */
    { .default_steps = {0x07d658f2, 0x07fa1819},},

    /* 141 ld_B_TDP_D */
    { .default_steps = {0x07d658f3, 0x07fa1819},},

    /* 142 ld_C_TDP_A */
    { .default_steps = {0x07d658f0, 0x07fa1829},},

    /* 143 ld_C_TDP_B */
    { .default_steps = {0x07d658f1, 0x07fa1829},},

    /* 144 ld_C_TDP_C */
    { .default_steps = {0x07d658f2, 0x07fa1829},},

    /* 145 ld_C_TDP_D */
    { .default_steps = {0x07d658f3, 0x07fa1829},},

    /* 146 ld_D_TDP_A */
    { .default_steps = {0x07d658f0, 0x07fa1839},},

    /* 147 ld_D_TDP_B */
    { .default_steps = {0x07d658f1, 0x07fa1839},},

    /* 148 ld_D_TDP_C */
    { .default_steps = {0x07d658f2, 0x07fa1839},},

    /* 149 ld_D_TDP_D */
    { .default_steps = {0x07d658f3, 0x07fa1839},},

    /* 14a push_SDP   */
    { .default_steps = {0x07c158ff, 0x077b58ff, 0x077b589c, 0x07fb589b},},

    /* 14b pop_SDP    */
    { .default_steps = {0x07bb58b9, 0x07bb58c9, 0x07c858ff},},

    /* 14c push_TDP   */
    { .default_steps = {0x07c658ff, 0x077b58ff, 0x077b589c, 0x07fb589b},},

    /* 14d pop_TDP    */
    { .default_steps = {0x07bb58b9, 0x07bb58c9, 0x07f058ff},},

    /* 14e tst_A      */
    { .default_steps = {0x07ff18f0},},

    /* 14f tst_B      */
    { .default_steps = {0x07ff18f1},},

    /* 150 tst_C      */
    { .default_steps = {0x07ff18f2},},

    /* 151 tst_D      */
    { .default_steps = {0x07ff18f3},},

    /* 152 st_SDP_A   */
    { .default_steps = {0x07b95890},},

    /* 153 st_SDP_B   */
    { .default_steps = {0x07b95891},},

    /* 154 st_SDP_C   */
    { .default_steps = {0x07b95892},},

    /* 155 st_SDP_D   */
    { .default_steps = {0x07b95893},},

    /* 156 ld_A_TDP_imm */
    { .default_steps = {0x07bd58b9, 0x17d658fb, 0x07fa1809},},

    /* 157 ld_A_SDP_imm */
    { .default_steps = {0x07bd58b9, 0x17d158fb, 0x07fa1809},},

    /* 158 ld_B_TDP_imm */
    { .default_steps = {0x07bd58b9, 0x17d658fb, 0x07fa1819},},

    /* 159 ld_B_SDP_imm */
    { .default_steps = {0x07bd58b9, 0x17d158fb, 0x07fa1819},},

    /* 15a ld_C_TDP_imm */
    { .default_steps = {0x07bd58b9, 0x17d658fb, 0x07fa1829},},

    /* 15b ld_C_SDP_imm */
    { .default_steps = {0x07bd58b9, 0x17d158fb, 0x07fa1829},},

    /* 15c ld_D_TDP_imm */
    { .default_steps = {0x07bd58b9, 0x17d658fb, 0x07fa1839},},

    /* 15d ld_D_SDP_imm */
    { .default_steps = {0x07bd58b9, 0x17d158fb, 0x07fa1839},},

    /* 15e st_TDP_imm_A */
    { .default_steps = {0x07bd58b9, 0x17d658fb, 0x07fa5890},},

    /* 15f st_TDP_imm_B */
    { .default_steps = {0x07bd58b9, 0x17d658fb, 0x07fa5891},},

    /* 160 st_TDP_imm_C */
    { .default_steps = {0x07bd58b9, 0x17d658fb, 0x07fa5892},},

    /* 161 st_TDP_imm_D */
    { .default_steps = {0x07bd58b9, 0x17d658fb, 0x07fa5893},},

    /* 162 st_SDP_imm_A */
    { .default_steps = {0x07bd58b9, 0x17d158fb, 0x07fa5890},},

    /* 163 st_SDP_imm_B */
    { .default_steps = {0x07bd58b9, 0x17d158fb, 0x07fa5891},},

    /* 164 st_SDP_imm_C */
    { .default_steps = {0x07bd58b9, 0x17d158fb, 0x07fa5892},},

    /* 165 st_SDP_imm_D */
    { .default_steps = {0x07bd58b9, 0x17d158fb, 0x07fa5893},},
};
