Velko/8-bit-CPU/bios/bios.asm

#include "types.def"
#include "instructions.def"
#include "ports.def"

#const(noemit) RAM_START = 0x0000
#const(noemit) STACK_END = 0xC010

#bankdef bios
{
    #bits 8
    #addr 0xE000
    #outp 0 * 8
    #addr_end 0x10000
    #fill
}

; Startup code, is executed after reset
; * initialize GP registers to zero (nice default)
; * load SP to dedicated stack area
; * jump to RAM location where the program should be loaded
__start:
    ldi A, 0 ; load 0 explicitly, because VerilogVM has X there by default and freaks out
    mov B, A ; when clr (essentially xor A, A) is tried. Should not been a problem on real hw.
    mov C, A
    mov D, A
    lea SP, STACK_END
    jmp RAM_START


#include "uart.asm"
#include "convert.asm"
