Velko/8-bit-CPU/turbo/core/src/gp_register.rs

use crate::router::{MainBusSource, ALULSource, ALURSource};
use crate::devices::{BusOutputPin, DelayedPin};
use crate::devices::GlobalSignalsReceiver;
use crate::devices::ValueSource;
use crate::runtime_state::BusValues;

pub struct GPRegister {
    pub name: &'static str,
    value_primary: u8,
    value_secondary: u8,
    pub out: BusOutputPin<MainBusSource>,
    pub load: DelayedPin,
    pub alu_l: BusOutputPin<ALULSource>,
    pub alu_r: BusOutputPin<ALURSource>,
}

impl GlobalSignalsReceiver for GPRegister {
    fn on_clock_tick_primary(&mut self, bus_values: &mut BusValues) {
        if self.load.is_enabled() {
            self.value_primary = bus_values.main_bus.value.unwrap();
        }
    }
    fn on_clock_tick_secondary(&mut self) {
        if self.value_primary != self.value_secondary {
            self.value_secondary = self.value_primary;
        }
    }
    fn on_reset(&mut self) {
        self.value_primary = 0;
        self.value_secondary = 0;
    }
}

impl ValueSource<u8> for GPRegister {
    fn get_value(&self, _bus_values: &BusValues) -> u8 {
        self.value_secondary
    }
}

impl GPRegister {
    pub fn new(name: &'static str, main_id: MainBusSource, alu_l_id: ALULSource, alu_r_id: ALURSource) -> Self {
        Self {
            name,
            value_primary: 0,
            value_secondary: 0,
            out: BusOutputPin::new(main_id),
            load: DelayedPin::new(),
            alu_l: BusOutputPin::new(alu_l_id),
            alu_r: BusOutputPin::new(alu_r_id),
        }
    }

    pub fn set_value(&mut self, value: u8) {
        self.value_primary = value;
        self.value_secondary = value;
    }
}


#[cfg(test)]
mod tests {
    use super::*;
    use crate::test_helpers::TestBench;
    use crate::router::{LoadMux, OutMux};
    use crate::control_word::ControlWordBuilder;
    use crate::router::DEFAULT_CW;

    #[test]
    fn test_gp_register() {
        let mut args = BusValues::new();
        args.main_bus.value = Some(42);
        let mut gp_reg = GPRegister::new("GP1", MainBusSource::A, ALULSource::A, ALURSource::A);

        // Simulate loading a value into the register
        gp_reg.load.change(&mut args, true);
        gp_reg.on_clock_tick_primary(&mut args);
        assert_eq!(gp_reg.value_primary, 42);
        assert_eq!(gp_reg.value_secondary, 0); // value_secondary should not change yet

        // Simulate clock tick secondary
        gp_reg.on_clock_tick_secondary();
        assert_eq!(gp_reg.value_secondary, 42);
    }

    #[test]
    fn test_load_a() {
        let mut bench = TestBench::new();
        let load_a_cw = ControlWordBuilder::default()
            .apply_mux::<LoadMux>(LoadMux::VALUE_A_LOAD)
            .build(); // load_A

        bench.devices.route_word(&mut bench.bus_values, DEFAULT_CW, load_a_cw);
        bench.bus_values.main_bus.value = Some(42); // Simulate loading 42 into A

        bench.devices.broadcast_clock_tick_primary(&mut bench.bus_values);
        bench.devices.broadcast_clock_tick_secondary();

        assert_eq!(42, bench.devices.A.value_secondary); // Check if A has the value 42 after clock tick
    }

    #[test]
    fn test_output_reg_value() {
        let mut bench = TestBench::new();

        bench.devices.A.set_value(42);

        let out_a_cw =  ControlWordBuilder::default()
            .apply_mux::<OutMux>(OutMux::VALUE_A_OUT)
            .build(); // out_A
        bench.devices.route_word(&mut bench.bus_values, DEFAULT_CW, out_a_cw);

        bench.bus_values.resolve(&bench.devices);

        assert_eq!(Some(42), bench.bus_values.main_bus.value); // Check if the main bus has the value 42 after out_A
    }

    #[test]
    fn test_copy_a_to_b() {
        let mut bench = TestBench::new();

        // Load 42 into A
        bench.devices.A.set_value(42);

        // Enable A Out and B Load
        let copy_a_to_b_cw = ControlWordBuilder::default()
            .apply_mux::<OutMux>(OutMux::VALUE_A_OUT)
            .apply_mux::<LoadMux>(LoadMux::VALUE_B_LOAD)
            .build();
        bench.devices.route_word(&mut bench.bus_values, DEFAULT_CW, copy_a_to_b_cw);

        // Simulate clock tick
        bench.bus_values.resolve(&bench.devices);
        bench.devices.broadcast_clock_tick_primary(&mut bench.bus_values);
        bench.devices.broadcast_clock_tick_secondary();

        assert_eq!(42, bench.devices.B.value_secondary); // Check if B has the value 42 after clock tick
    }
}
