Velko/8-bit-CPU/turbo/core/src/lib.rs

mod router;
mod devices;
mod gp_register;
mod temp_register;
mod alu;
mod flags;
mod program_counter;
mod control_word;
mod wo_register;
mod memory;
mod runtime_state;
mod cpu;
mod transfer_register;
mod stack_pointer;
mod clock;
mod step_counter;
mod address_register;
mod address_calculator;
mod io_controller;
mod trap_reason;
mod control_rom;
mod const_arg;

pub use control_word::ControlWord;
pub use router::DeviceMap;
pub use router::DEFAULT_CW;
pub use runtime_state::BusValues;
pub use cpu::Cpu;
pub use trap_reason::TrapReason;
pub use control_rom::ControlROM;
pub use io_controller::IOPorts;
pub use const_arg::ConstArg;

#[cfg(test)]
mod test_helpers;
