Velko/8-bit-CPU/emulator/cpu-modules/uart.v

module uart(
    inout [7:0] io_bus,
    input sel_data,
    input sel_status,
    input rnw,
    input clk
);

    reg [7:0] in_data;
    reg [7:0] status;

    initial begin
        status <= 8'b0;
    end

    always @(posedge clk) begin
        if (sel_data && !rnw) begin
            $hdb_send_char(2, io_bus);
        end
    end

    always @(negedge clk) begin
        if (sel_data && rnw) begin
            $hdb_discard_char(2);
        end
    end

    always @(posedge sel_status or posedge rnw) begin
        if (sel_status && rnw) begin
            $hdb_check_input(2, status);
        end
    end

    always @(posedge sel_data or posedge rnw) begin
        if (sel_data && rnw) begin
            $hdb_peek_char(2, in_data);
        end
    end

    wire [7:0] read_outp = sel_data ? in_data : status;
    assign io_bus = rnw && (sel_data || sel_status) ? read_outp : 8'bZ;

endmodule
