Velko/8-bit-CPU/turbo/core/src/peripherals.rs

use crate::{IOMessage, display_lcd::Lcd, IOPorts, uart::Uart};

pub struct Peripherals {
    display_numeric: DisplayNumeric,
    display_char: DisplayChar,
    lcd: Lcd,
    uart: Uart,
}

impl Peripherals {
    pub fn new() -> Self {
        Self {
            display_numeric: DisplayNumeric::new(),
            display_char: DisplayChar::new(),
            lcd: Lcd::new(),
            uart: Uart::new(),
        }
    }
}

impl IOPorts for Peripherals {
    fn read_port(&self, port: u8) -> u8 {
        match port {
            0x11 => self.lcd.get_status(),
            0x20 => self.uart.get_status(),
            0x21 => self.uart.get_char(),
            _ => todo!("Port: 0x{:02x} input not yet implemented", port),
        }
    }

    fn write_port(&mut self, port: u8, value: u8) -> Option<IOMessage> {
        match port {
            0 => {
                return Some(IOMessage::Out { payload: self.display_numeric.format(value), port: port });
            },
            1 => {
                self.display_numeric.set_mode(value);
            },
            4 => {
                return Some(IOMessage::Out { payload: self.display_char.format(value), port: port });
            },
            0x10 => {
                if let Some(msg) = self.lcd.send_data(value) {
                    return Some(IOMessage::Out { payload: msg, port: port });
                }
            },
            0x11 => {
                self.lcd.send_command(value);
            },
            0x21 => {
                self.uart.send_char(value);
            },
            _ => todo!("Port: 0x{:02x} not yet implemented", port),
        }
        None
    }
}

struct DisplayNumeric {
    mode: u8,
}

impl DisplayNumeric {
    pub fn new() -> Self {
        Self { mode: 0 }
    }

    pub fn format(&self, value: u8) -> String {
        match self.mode {
            0 => format!("{:4}\\n", value),
            1 => format!("{:4}\\n", value as i8),
            2 => format!("h {:02x}\\n", value),
            3 => format!("o{:03o}\\n", value),
            _ => panic!("DisplayNumeric: unsupported mode {}", self.mode),
        }
    }

    pub fn set_mode(&mut self, mode: u8) {
        self.mode = mode;
    }
}

struct DisplayChar {
}

impl DisplayChar {
    pub fn new() -> Self {
        Self {}
    }

    pub fn format(&self, value: u8) -> String {
        format!("{}", value as char)
    }
}
