Velko/8-bit-CPU/emulator/cpu-modules/display_char.v

module display_char(
    inout [7:0] main_bus,
    input clk,
    input load_val
);

    reg [159:0] out_fmt;

    always @(posedge clk) begin
        if (load_val) begin
            if (main_bus == "\n") begin
                $swrite(out_fmt, "#OUT#4#\\n");
            end
            else begin
                $sformat(out_fmt, "#OUT#4#%c", main_bus);
            end
            $hdb_send_str(0, out_fmt);
        end
    end

endmodule
