Velko/8-bit-CPU/emulator/cpu-modules/address_calc.v

module address_calc (
    input outn,
    input loadn,
    input m_sign,

    input clk,

    inout [15:0] abus,
    input [7:0] mbus
);

    wire [15:0] out_v;
    wire [15:0] add_v;
    wire [3:0] sign_ext;

    dff_377 outst_0(.cp(clk), .en(loadn), .d(add_v[7:0]), .q(out_v[7:0]));
    dff_377 outst_1(.cp(clk), .en(loadn), .d(add_v[15:8]), .q(out_v[15:8]));

    adder_283 add_0(.a(abus[3:0]), .b(mbus[3:0]), .cin(1'b0), .s(add_v[3:0]));
    adder_283 add_1(.a(abus[7:4]), .b(mbus[7:4]), .cin(add_0.cout), .s(add_v[7:4]));
    adder_283 add_2(.a(abus[11:8]), .b(sign_ext), .cin(add_1.cout), .s(add_v[11:8]));
    adder_283 add_3(.a(abus[15:12]), .b(sign_ext), .cin(add_2.cout), .s(add_v[15:12]));

    buffer_245 out_0(.oen(outn), .dir(1'b1), .a(out_v[7:0]), .b(abus[7:0]));
    buffer_245 out_1(.oen(outn), .dir(1'b1), .a(out_v[15:8]), .b(abus[15:8]));

    and_08p sign_and (
        .a1(mbus[7]),
        .b1(m_sign),

        .a2(1'b0),
        .b2(1'b0),

        .a3(1'b0),
        .b3(1'b0),

        .a4(1'b0),
        .b4(1'b0)
    );

    assign sign_ext = {sign_and.y1, sign_and.y1, sign_and.y1, sign_and.y1};

endmodule
