Velko/8-bit-CPU/emulator/chips/nand_10p.v

module nand_10p (
    input a1,
    input b1,
    input c1,
    output y1,

    input a2,
    input b2,
    input c2,
    output y2,

    input a3,
    input b3,
    input c3,
    output y3);

    assign y1 = !(a1 & b1 & c1);
    assign y2 = !(a2 & b2 & c2);
    assign y3 = !(a3 & b3 & c3);

    /* Instantiation:
    nand_10p new_instance (
        .a1(),
        .b1(),
        .c1(),
        .y1(),

        .a2(),
        .b2(),
        .c2().
        .y2(),

        .a3(),
        .b3(),
        .c3(),
        .y3()
    );
    */
endmodule
