Velko/8-bit-CPU/emulator/cpu-modules/address_counter.v

module address_counter (
    input outn,
    input loadn,
    input cupn,
    input cdownn,

    input clk,
    input iclk,
    input resetn,

    inout [15:0] abus
);

    wire [15:0] addr;
    wire clocked_load;
    wire res_load;
    wire p_loadn;
    wire cpu;
    wire cpd;
    wire n_clk;
    wire gated_count;

    // pl should follow !clk, when loadn == low
    // pl should follow resetn
    // cpu should follow !clk, when cup == enabled (low) and outn == enabled (low)

    // pl = (not(clk) or loadn) and resetn
    // pl = not((not(clk) or loadn) nand resetn)
    // cpu = not(clk) or cupn or outn
    // cpd = not(clk) or cdownn or outn
    nand_00p inv(
        .a1(clk), .b1(clk), .y1(n_clk),
        .a2(clocked_load), .b2(resetn), .y2(res_load),
        .a3(res_load), .b3(res_load), .y3(p_loadn),
        .a4(1'b0), .b4(1'b0));

    or_32p ctrl(
        .a1(n_clk), .b1(outn), .y1(gated_count),
        .a2(n_clk), .b2(loadn), .y2(clocked_load),
        .a3(gated_count), .b3(cupn), .y3(cpu),
        .a4(gated_count), .b4(cdownn), .y4(cpd));

    udcounter_193 cnt_0(
        .mr(1'b0),
        .pl(p_loadn),
        .d(abus[3:0]),
        .q(addr[3:0]),
        .cpu(cpu),
        .cpd(cpd));

    udcounter_193 cnt_1(
        .mr(1'b0),
        .pl(p_loadn),
        .d(abus[7:4]),
        .q(addr[7:4]),
        .cpu(cnt_0.tcu),
        .cpd(cnt_0.tcd));

    udcounter_193 cnt_2(
        .mr(1'b0),
        .pl(p_loadn),
        .d(abus[11:8]),
        .q(addr[11:8]),
        .cpu(cnt_1.tcu),
        .cpd(cnt_1.tcd));

    udcounter_193 cnt_3(
        .mr(1'b0),
        .pl(p_loadn),
        .d(abus[15:12]),
        .q(addr[15:12]),
        .cpu(cnt_2.tcu),
        .cpd(cnt_2.tcd));

    dff_374 outst_0(
        .cp(iclk),
        .oen(outn),
        .d(addr[7:0]),
        .q(abus[7:0]));

    dff_374 outst_1(
        .cp(iclk),
        .oen(outn),
        .d(addr[15:8]),
        .q(abus[15:8]));

endmodule
