Velko/8-bit-CPU/arduino/pincontrol/prg_runner.cpp

#include <Arduino.h>
#include "shiftoutext.h"
#include "device_interface.h"
#include "microcode.h"
#include "op-defs.h"

extern DeviceInterface dev;

char txt_buf[80];

void reset_pc()
{
    /* write 0 into PC */
    dev.control.write16(APPLY_MUX(CTRL_DEFAULT, MUX_LOAD_MASK, MPIN_PC_LOAD_BITS));
    dev.mainBus.write(0);
    dev.clock.pulse();
    dev.inv_clock.pulse();

    /* release the bus */
    dev.mainBus.set_input();
}

uint8_t fetch_instruction()
{
    dev.control.write16(op_fetch[0]);
    dev.clock.pulse();
    dev.inv_clock.pulse();

    /* combine last fetch step with IRFETCH enable */
    dev.control.write16(op_fetch[1] ^ LPIN_IRFETCH_LOAD_BIT);
    dev.clock.pulse();
    dev.inv_clock.pulse();

    /* write it 2 times, to get the instruction from IR */
    dev.control.write16(CTRL_DEFAULT);
    uint8_t opcode = dev.control.write16(CTRL_DEFAULT);

    return opcode;
}

void execute_steps()
{
    for(;;)
    {
        uint8_t opcode = fetch_instruction();
        uint8_t flags = dev.flagsBus.read();

        delay(1);

        struct op_microcode instruction;

        memcpy_P(&instruction, &microcode[opcode], sizeof(struct op_microcode));

        uint16_t *steps = instruction.default_steps;

        /* currently only single flags_alt is allowed, this makes things simpler */
        if (instruction.f_alt[0].mask)
        {
            if ((flags & instruction.f_alt[0].mask) == instruction.f_alt[0].value)
                steps = instruction.f_alt[0].steps;
        }

        for (uint8_t i = 0; i < MAX_STEPS && steps[i]; ++i)
        {
            dev.control.write16(steps[i]);
            dev.clock.pulse();

            /* special handling to intercept output */
            if ((steps[i] & MUX_LOAD_MASK) ==  MPIN_OUT_LOAD_BITS)
            {
                uint8_t out_val = dev.mainBus.read();
                sprintf(txt_buf, "%d", out_val);
                Serial.println(txt_buf);
                delay(250);
            }

            dev.inv_clock.pulse();

            if ((steps[i] & LPIN_CLOCK_HALT_BIT) == 0)
            {
                Serial.println("Halted");
                return;
            }
        }
    }
}

void run_program()
{
    reset_pc();
    execute_steps();
}
