Velko/8-bit-CPU/emulator/chips/and_08p.v

module and_08p (
    input a1,
    input b1,
    output y1,

    input a2,
    input b2,
    output y2,

    input a3,
    input b3,
    output y3,

    input a4,
    input b4,
    output y4);

    assign y1 = a1 & b1;
    assign y2 = a2 & b2;
    assign y3 = a3 & b3;
    assign y4 = a4 & b4;

    /* Instantiation:
    and_08p new_instance (
        .a1(),
        .b1(),
        .y1(),

        .a2(),
        .b2(),
        .y2(),

        .a3(),
        .b3(),
        .y3(),

        .a4(),
        .b4(),
        .y4()
    );
    */
endmodule
