Velko/8-bit-CPU/arduino/pincontrol/device_interface.h

#ifndef DEVICE_INTERFACE_H
#define DEVICE_INTERFACE_H

#include "iobus8bit.h"
#include "iobus4bit.h"
#include "shiftoutext.h"
#include "clock.h"

class DeviceInterface
{
    public:
        DeviceInterface();
        void setup();
        IOBus8bit mainBus;
        IOBus4bit flagsBus;
        Clock clock;
        Clock inv_clock;
        ShiftOutExt control;
};



#endif /* DEVICE_INTERFACE_H */
