Velko/8-bit-CPU/arduino/xmprog/eeprom_ops.c

#include <stdio.h>
#include <avr/pgmspace.h>
#include <util/delay.h>
#include "eeprom_ops.h"
#include "eeprom_hw.h"
#include "addr_port.h"
#include "ctrl_pins.h"

FILE eeprom_stream;
uint32_t eeprom_addr;
uint32_t eeprom_size;

static uint8_t eeprom_wait_dq7(uint8_t data);

static void eeprom_write(uint16_t addr, uint8_t value)
{
    uint8_t old_value = eeprom_read_addr(addr);

    /* Only if new value differs */
    if (old_value != value)
    {
        do {
            eeprom_peform_write(addr, value);
        }
        while (!eeprom_wait_dq7(value));
    }
}

#define MAX_POLL 0xFFFF

static uint8_t eeprom_wait_dq7(uint8_t data)
{
    data &= 0x80; // interested only in bit 7

    uint16_t repeats;
    // read repeatedly until bit 7 returns "true data" or too many attempts
    for (repeats = 0; (data != (eeprom_read() & 0x80)) && repeats < MAX_POLL; ++repeats)
        _delay_us(1);

    return repeats < MAX_POLL;  // true if success
}

void eeprom_erase_all(struct chip_def *chip, bool force)
{
    /* EEPROMs do not need to be erased before read, unless requested explicitly */
    if (!force) return;

    ctrl_chip_select(chip->socket);
    eeprom_size = chip->size;

    for (uint16_t addr = 0; addr < eeprom_size; ++addr)
    {
        eeprom_write(addr, 0xFF);
    }
}

static int eeprom_getc(FILE *stream)
{
    /* trying to read past end */
    if (eeprom_addr >= eeprom_size)
        return _FDEV_EOF;

    return eeprom_read_addr(eeprom_addr++);
}

static int eeprom_putc(char c, FILE *stream)
{
    /* trying to write past end */
    if (eeprom_addr >= eeprom_size)
        return _FDEV_ERR;

    eeprom_write(eeprom_addr++, c);
    return 0;
}

FILE *eeprom_open(struct chip_def *chip)
{
    ctrl_chip_select(chip->socket);

    fdev_setup_stream(&eeprom_stream, eeprom_putc, eeprom_getc, _FDEV_SETUP_RW);

    eeprom_addr = 0;
    eeprom_size = chip->size;

    return &eeprom_stream;
}
