Velko/8-bit-CPU/arduino/xmprog/ctimer.h

#ifndef CTIMER_H
#define CTIMER_H


#ifdef __cplusplus
extern "C" {
#endif

    void ctimer_init();
    void ctimer_start();
    void ctimer_stop();


#ifdef __cplusplus
}
#endif


#endif /* CTIMER_H */
