Velko/8-bit-CPU/arduino/eeprom_burner/help_page.ino

void display_help()
{
    Serial.println(F("Valid commands are:"));
    Serial.println(F("    help   - display this page"));
    Serial.println(F("    digits - burn digits"));
    Serial.println(F("    erase  - erase all contents"));
    Serial.println(F("    read   - read all contents"));
}
