Velko/8-bit-CPU/emulator/tests/tb_alu_and.v

module tb_alu_and;

    reg [7:0] input_l;
    reg [7:0] input_r;
    reg outn;

    integer i;

    alu_and alu(.arg_l(input_l), .arg_r(input_r), .outn(outn));

    initial begin
        $display("ALU And...");
        input_l <= 0;
        input_r <= 0;

        outn <= 1;

        // output disabled initially
        #1
        `assert(alu.bus, 8'bZ);

        // AND from LHS
        outn <= 0;
        input_r <= 8'hff;
        for (i = 0; i < 8 ; i = i + 1) begin
            input_l <= (8'b1 << i);
            #1
            `assert(alu.bus, (8'b1 << i));
        end

        // AND from RHS
        input_l <= 8'hff;
        for (i = 0; i < 8 ; i = i + 1) begin
            input_r <= (8'b1 << i);
            #1
            `assert(alu.bus, (8'b1 << i));
        end
    end

endmodule
