Velko/8-bit-CPU/emulator/tests/tb_address_calc.v

module tb_address_calc;

    wire [15:0] abus;
    reg waddr;
    reg [15:0] addr;

    reg [7:0] mbus;

    reg clk;
    reg outn;
    reg loadn;
    reg m_sign;

    address_calc acalc(
        .abus(abus),
        .mbus(mbus),

        .clk(clk),

        .outn(outn),
        .loadn(loadn),
        .m_sign(m_sign)
    );

initial begin
    $display("Address calculator...");

    waddr <= 0;
    clk <= 0;
    outn <= 1;
    loadn <= 1;
    #1

    /* 64737 + 168 signed */
    addr <= 16'd64737;
    mbus <= 8'd168;
    waddr <= 1;
    loadn <= 0;
    m_sign <= 1;

    #1
    `tick(clk);

    waddr <= 0;
    outn <= 0;
    loadn <= 1;
    #1

    `assert(abus, 16'd64649);
    outn <= 1;

    /* 64737 + 168 unsigned */
    waddr <= 1;
    loadn <= 0;
    m_sign <= 0;

    #1
    `tick(clk);

    waddr <= 0;
    outn <= 0;
    loadn <= 1;
    #1

    `assert(abus, 16'd64905);
end

    assign abus = waddr ? addr : 16'bz;

endmodule
